joeldushouyu/ExternalGraphicCard/ImageForDocumentation/sideViewOfAssembledVersion.jpg

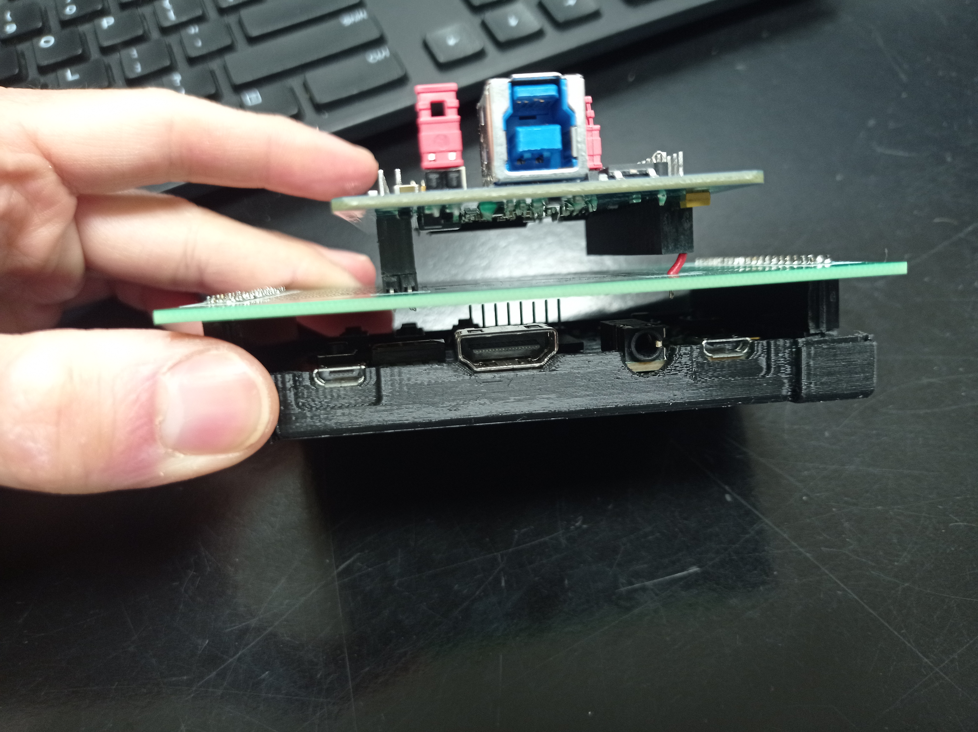
ImageForDocumentation/sideViewOfAssembledVersion.jpg
