joeldushouyu/ExternalGraphicCard/ImageForDocumentation/StepForGPIFII/13.png

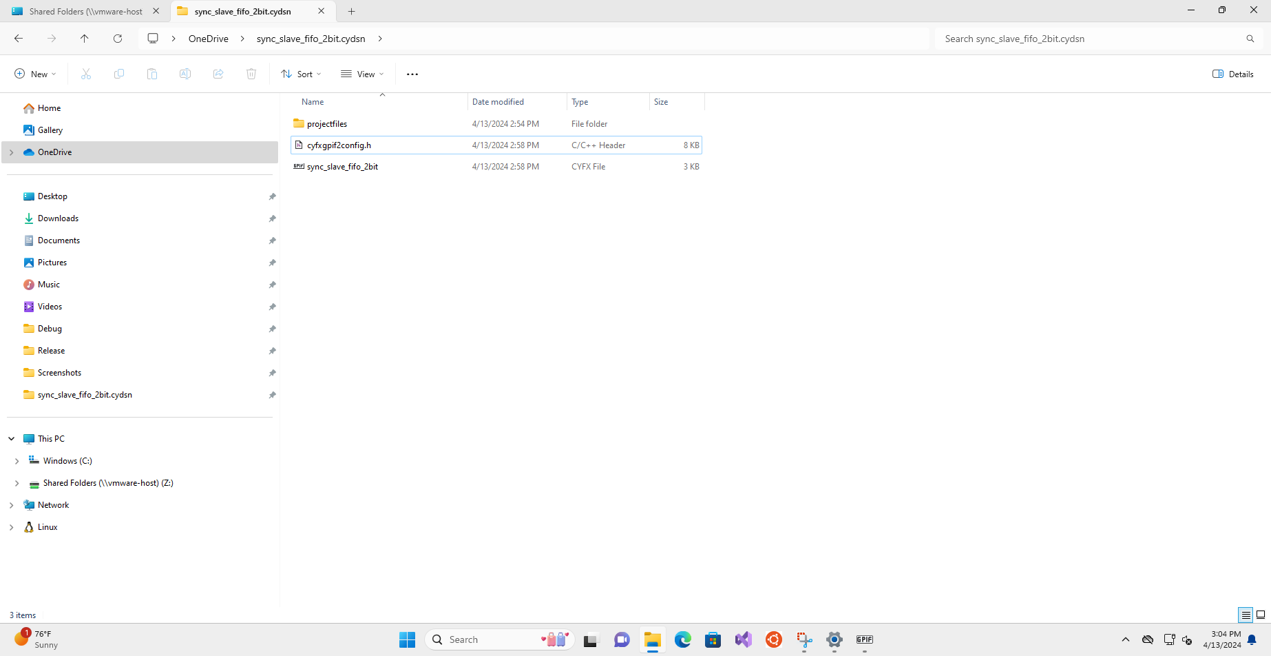
ImageForDocumentation/StepForGPIFII/13.png
