joeldushouyu/ExternalGraphicCard/ImageForDocumentation/StepForLoadingToCypressFx3/7.png

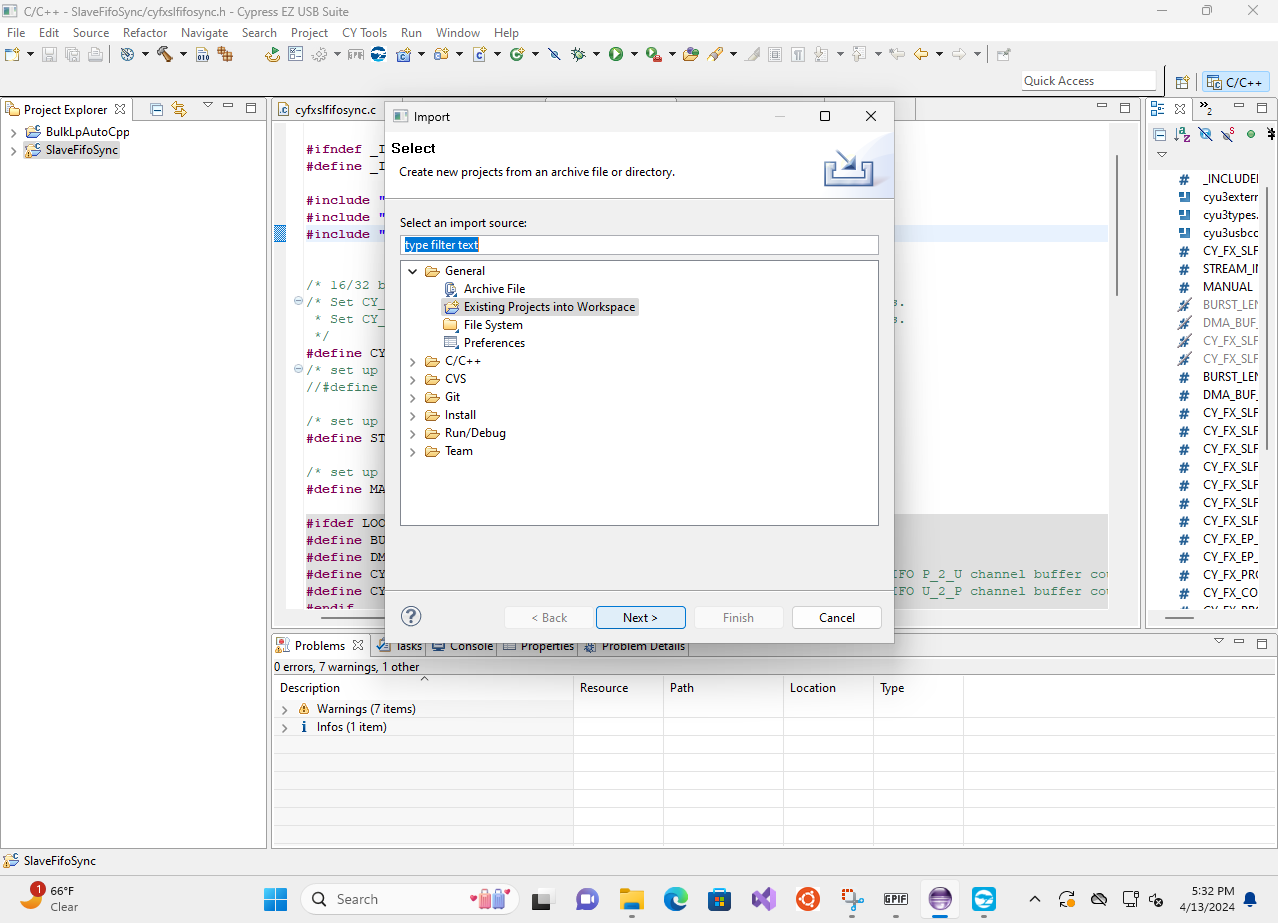
ImageForDocumentation/StepForLoadingToCypressFx3/7.png
