joeldushouyu/ExternalGraphicCard/ImageForDocumentation/StepForLoadingToCypressFx3/8.png

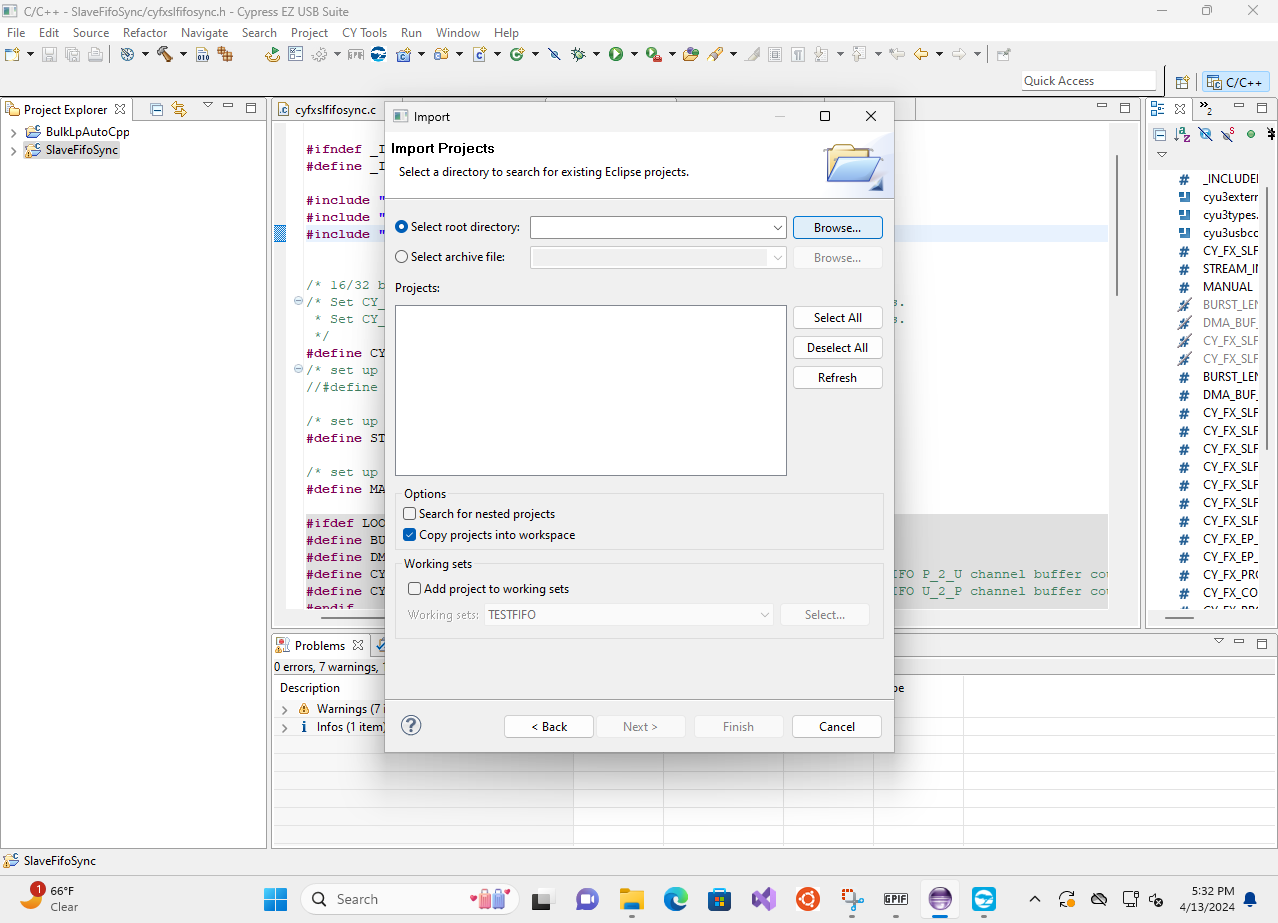
ImageForDocumentation/StepForLoadingToCypressFx3/8.png
