joeldushouyu/ExternalGraphicCard/ImageForDocumentation/TopViewOfHalfAssembled.jpg

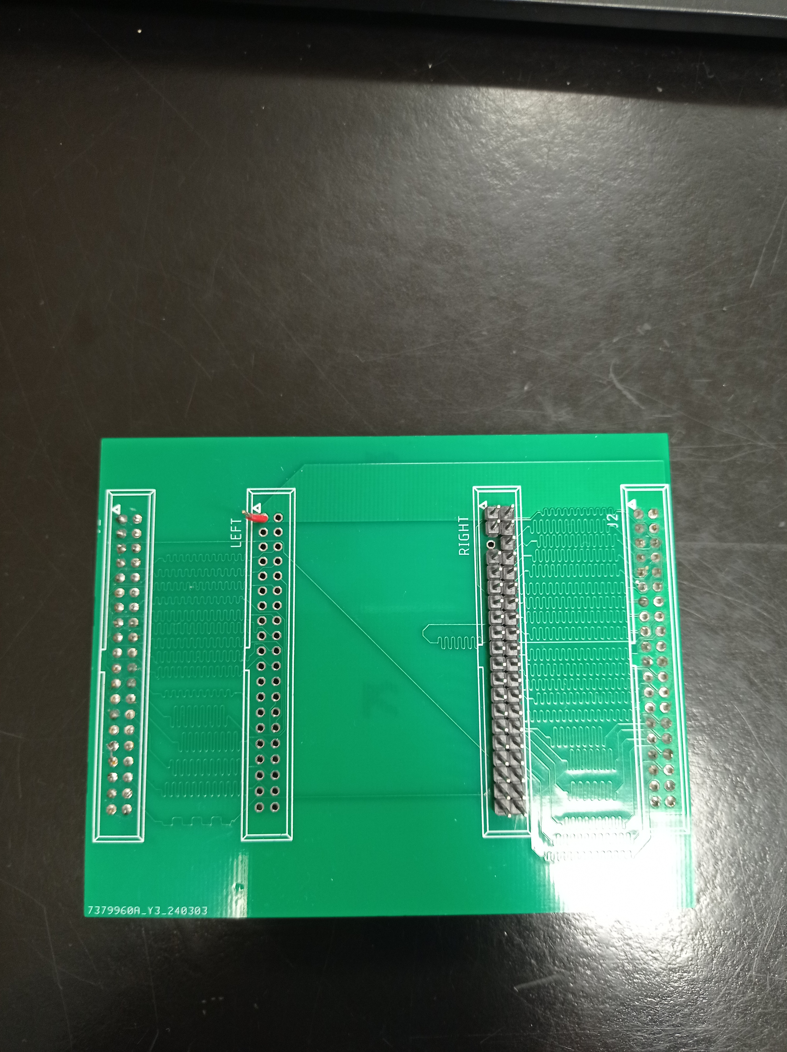
ImageForDocumentation/TopViewOfHalfAssembled.jpg
